furpectfox/Op-Amp-Based-Lithium-Charger/KiCad/LiPo_Charger.kicad_pcb

## KiCad design hardware/board.kicad_sch

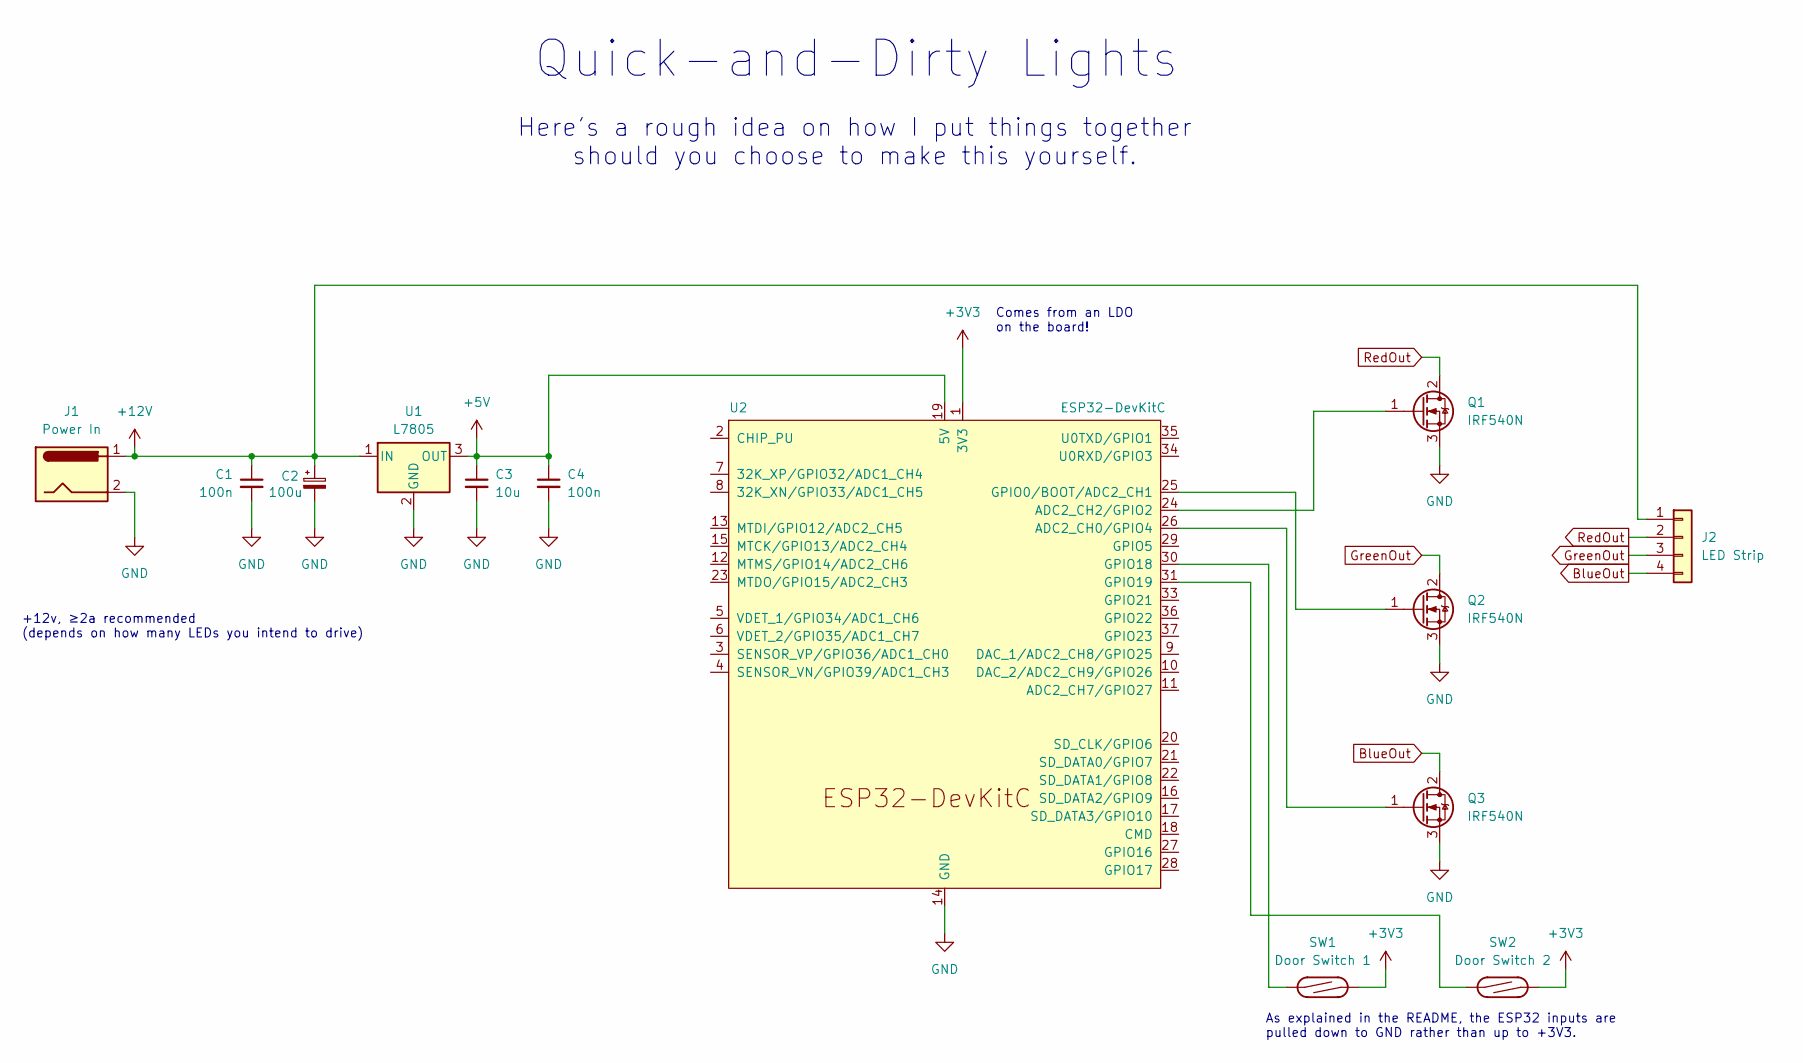
[picture p10: schematic board.kicad_sch]

Parts:
C1, C4: 100n; C_0603_1608Metric
C2: 100u; CP_Elec_6.3x7.7
C3: 10u; C_0603_1608Metric
J1: Power In
J2: LED Strip
Q1, Q2, Q3: IRF540N; TO-220-3_Vertical
SW1: Door Switch 1
SW2: Door Switch 2
U1: L7805
U2: ESP32-DevKitC

Connections:
+3V3: SW1.2, SW2.2, U2.1 (3V3)
+5V: C3.1, C4.1, U1.3 (OUT), U2.19 (5V)
+12V: C1.1, C2.1, J1.1, J2.1, U1.1 (IN)
BlueOut: J2.4, Q3.2 (D)
GND: C1.2, C2.2, C3.2, C4.2, J1.2, Q1.3 (S), Q2.3 (S), Q3.3 (S), U1.2 (GND), U2.14 (GND), U2.32 (GND), U2.38 (GND)
GreenOut: J2.3, Q2.2 (D)
unnamed: Q1.1 (G), U2.24 (ADC2_CH2/GPIO2)
unnamed: Q2.1 (G), U2.25 (GPIO0/BOOT/ADC2_CH1)
unnamed: Q3.1 (G), U2.26 (ADC2_CH0/GPIO4)
unnamed: SW1.1, U2.30 (GPIO18)
unnamed: SW2.1, U2.31 (GPIO19)
RedOut: J2.2, Q1.2 (D)

Notes on the sheet:
Quick-and-Dirty Lights
+12v, ≥2a recommended (depends on how many LEDs you intend to drive)
As explained in the README, the ESP32 inputs are pulled down to GND rather than up to +3V3.
Here's a rough idea on how I put things together should you choose to make this yourself.
Comes from an LDO on the board!
